align-racing-uia/electronic_throttle_controller/etbc_cad/Box_render_exploded.png

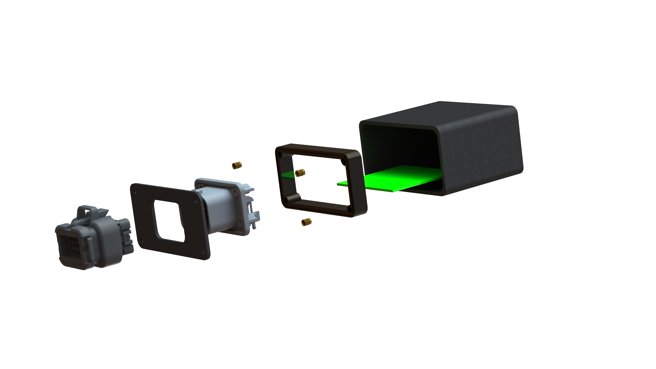
etbc_cad/Box_render_exploded.png
