align-racing-uia/electronic_throttle_controller/etbc_pcb/etbc_2019/AR19_ETBC/ETB_controller_v5.png

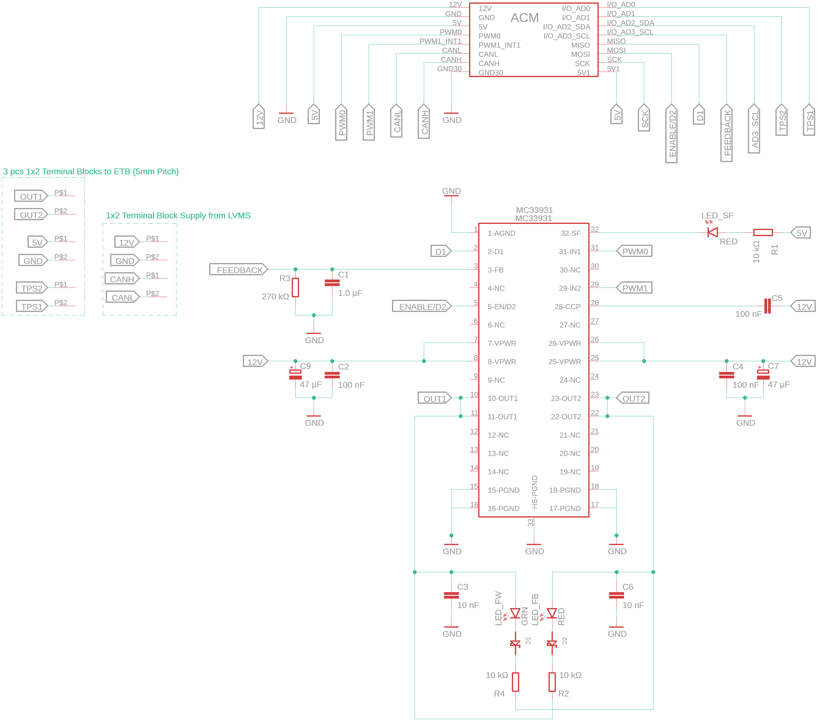
etbc_pcb/etbc_2019/AR19_ETBC/ETB_controller_v5.png
