align-racing-uia/electronic_throttle_controller/etbc_cad/PCB_HEATSINK.SLDPRT

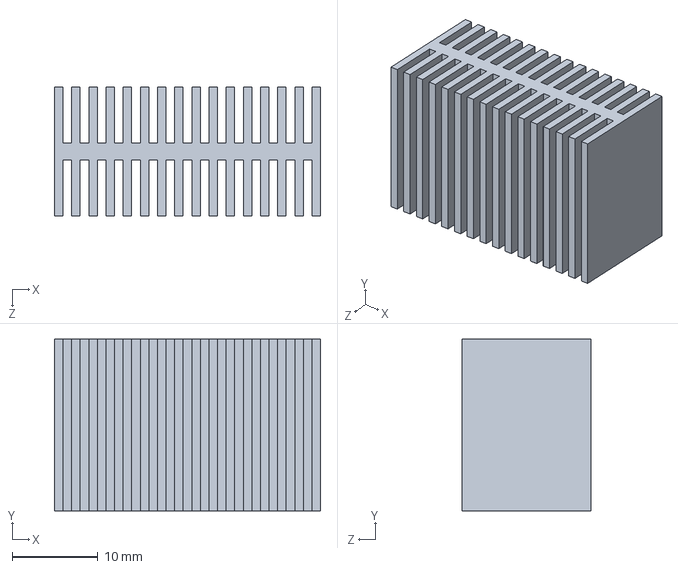
[picture p21: CAD file, 2021-08-01]
etbc_cad/PCB_HEATSINK.SLDPRT
31.0 x 20.0 x 15.0 mm
