align-racing-uia/electronic_throttle_controller/etbc_cad/AMP_14pin_panel_1-776267-1.SLDPRT

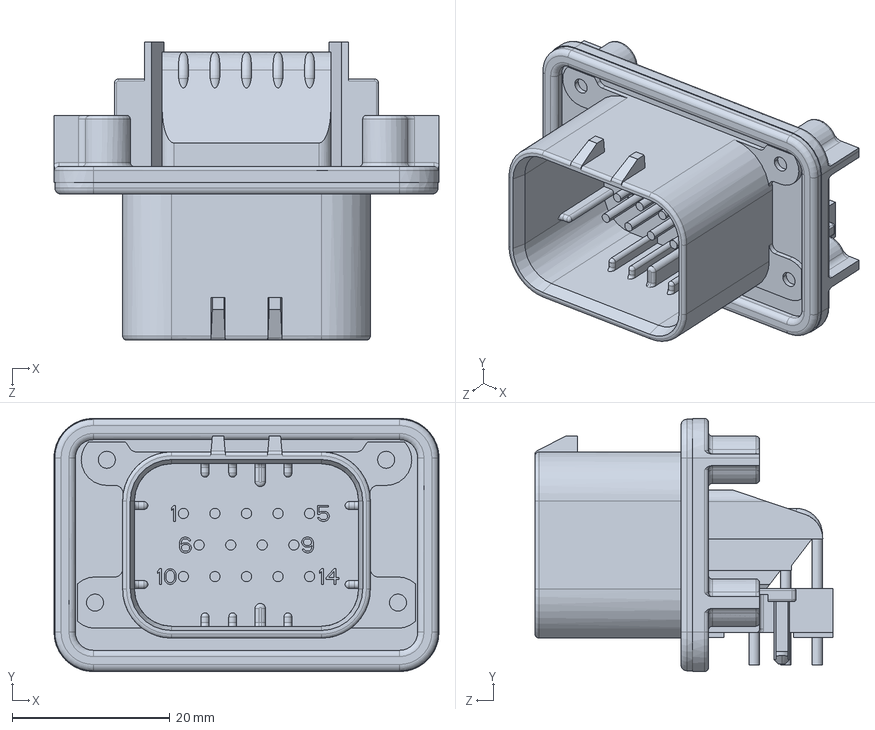
[picture p22: CAD file, 2021-08-01]
etbc_cad/AMP_14pin_panel_1-776267-1.SLDPRT
48.8 x 32.1 x 37.8 mm
