align-racing-uia/electronic_throttle_controller/etbc_cad/Threaded Insert.SLDPRT

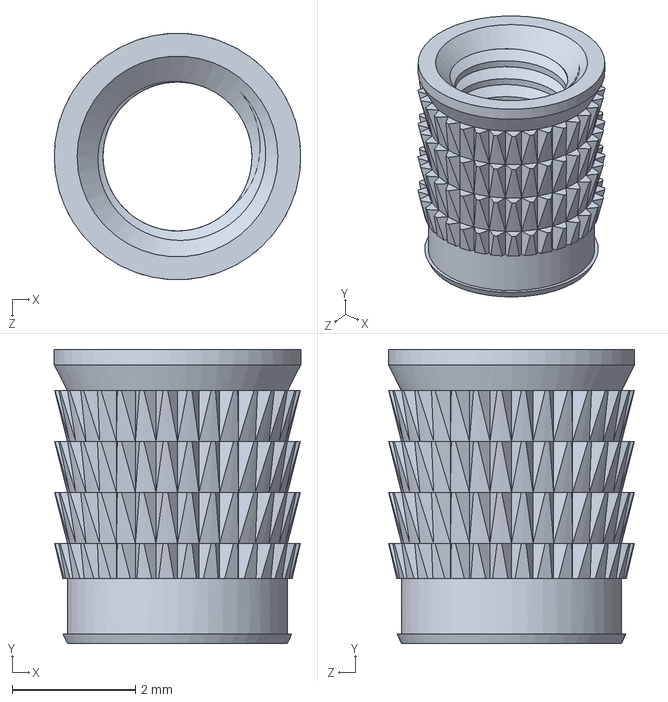
[picture p23: CAD file, 2021-08-01]
etbc_cad/Threaded Insert.SLDPRT
4.00 x 4.77 x 3.99 mm
