align-racing-uia/electronic_throttle_controller/etbc_code/ar19_etc_acm_etb/src/mcp2515/examples/wiring-diy.png

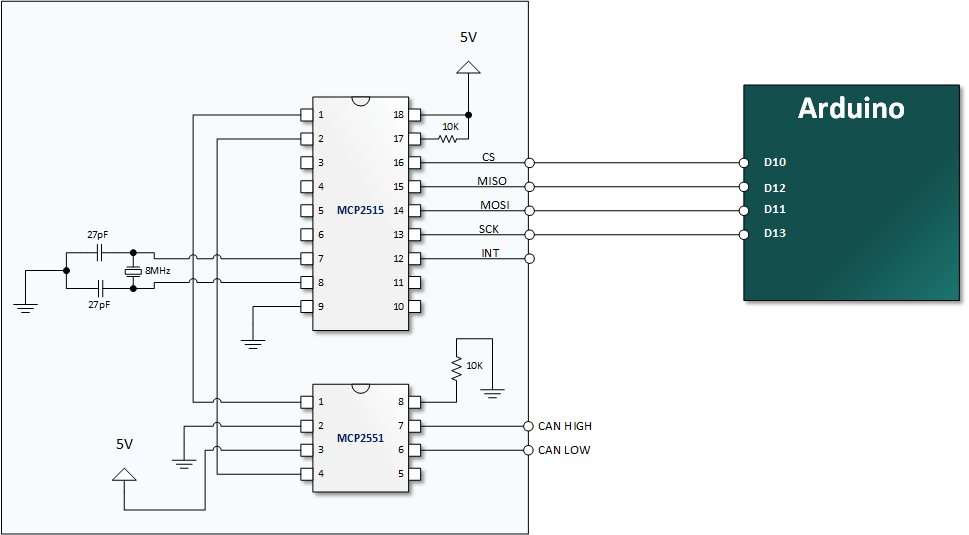
etbc_code/ar19_etc_acm_etb/src/mcp2515/examples/wiring-diy.png
